Veyniac/Pico-Audio-Interface/USB_Audio_Interface.kicad_sch

## KiCad design USB_Audio_Interface.kicad_sch (2025-06-18, last stored version)

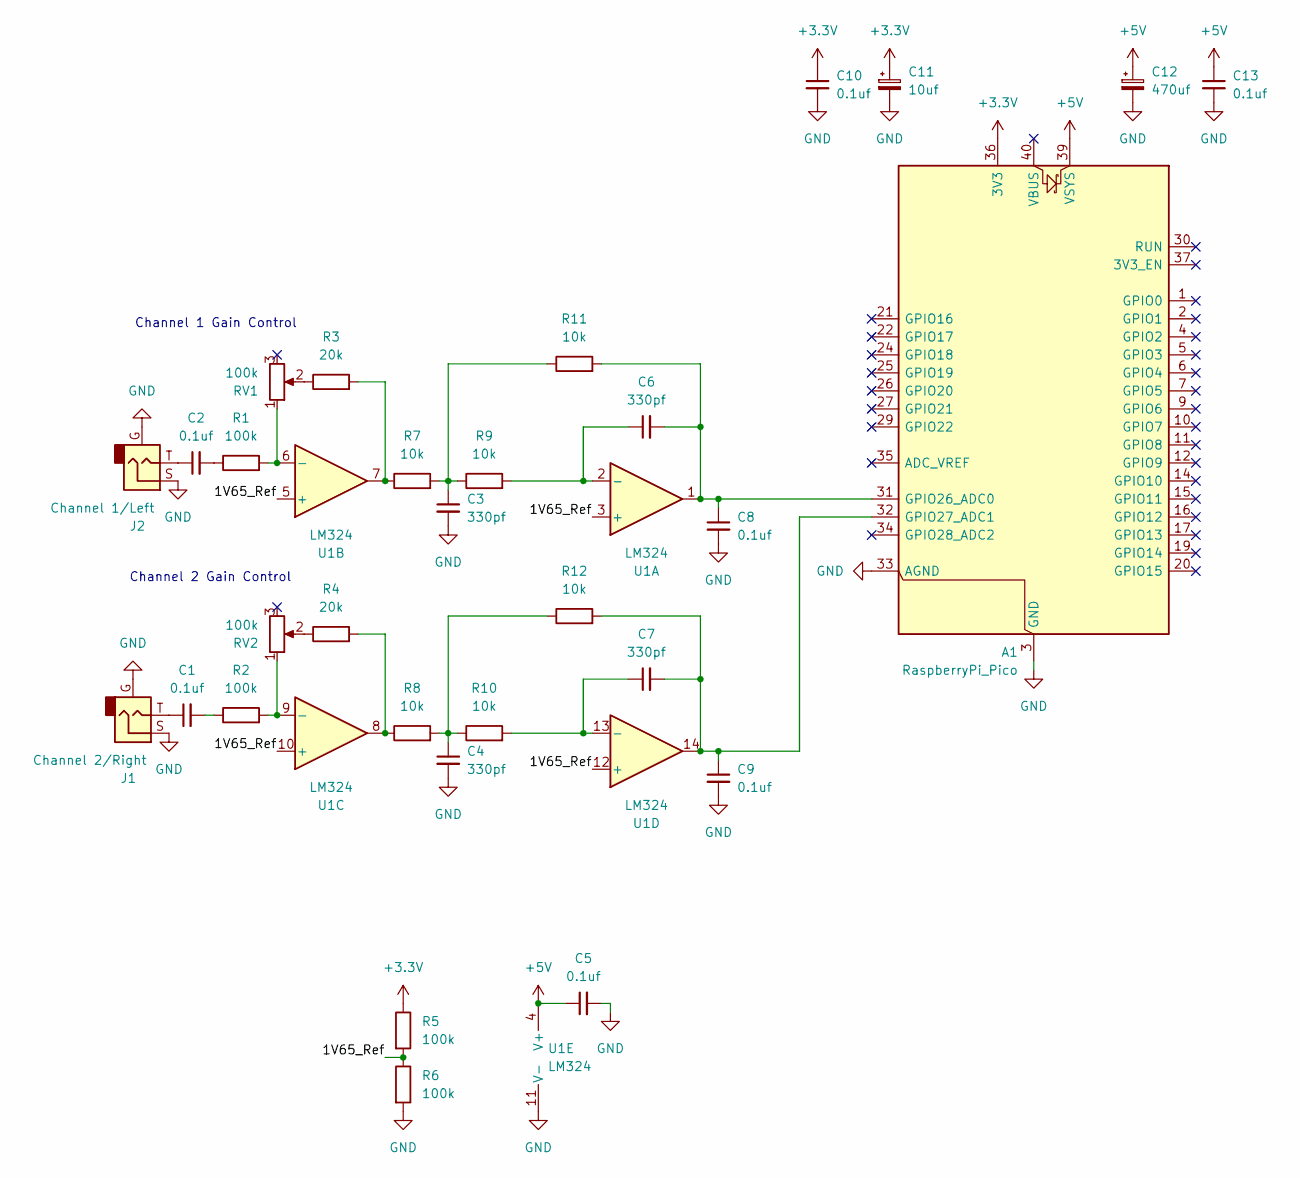
[picture p2: schematic USB_Audio_Interface.kicad_sch]

Parts:
A1: RaspberryPi_Pico; RaspberryPi_Pico_Common_Unspecified
C1, C2, C5, C8, C9, C10, C13: 0.1uf
C3, C4, C6, C7: 330pf
C11: 10uf
C12: 470uf
J1: Channel 2/Right
J2: Channel 1/Left
R1, R2, R5, R6: 100k
R3, R4: 20k
R7, R8, R9, R10, R11, R12: 10k
RV1, RV2: 100k
U1: LM324

Connections:
1V65_Ref: R5.2, R6.1, U1.3 (+), U1.5 (+), U1.10 (+), U1.12 (+)
+3.3V: A1.36 (3V3), C10.1, C11.1, R5.1
+5V: A1.39 (VSYS), C5.1, C12.1, C13.1, U1.4 (V+)
GND: A1.3 (GND), A1.8 (GND), A1.13 (GND), A1.18 (GND), A1.23 (GND), A1.28 (GND), A1.33 (AGND), A1.38 (GND), C3.2, C4.2, C5.2, C8.2, C9.2, C10.2, C11.2, C12.2, C13.2, J1.G, J1.S, J2.G, J2.S, R6.2, U1.11 (V-)
unnamed: A1.31 (GPIO26_ADC0), C6.2, C8.1, R11.2, U1.1
unnamed: A1.32 (GPIO27_ADC1), C7.2, C9.1, R12.2, U1.14
unnamed: C1.1, J1.T
unnamed: C1.2, R2.1
unnamed: C2.1, J2.T
unnamed: C2.2, R1.1
unnamed: C3.1, R7.2, R9.1, R11.1
unnamed: C4.1, R8.2, R10.1, R12.1
unnamed: C6.1, R9.2, U1.2 (-)
unnamed: C7.1, R10.2, U1.13 (-)
unnamed: R1.2, RV1.1, U1.6 (-)
unnamed: R2.2, RV2.1, U1.9 (-)
unnamed: R3.1, RV1.2
unnamed: R3.2, R7.1, U1.7
unnamed: R4.1, RV2.2
unnamed: R4.2, R8.1, U1.8

Notes on the sheet:
Channel 2 Gain Control
Channel 1 Gain Control
